Pongkemon01/weather-station/Inc/bsp_driver_sd.h

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
/* Define to prevent recursive inclusion -------------------------------------*/
#ifndef __STM32L4_SD_H
#define __STM32L4_SD_H

#ifdef __cplusplus
extern "C"
{
#endif

/* Includes ------------------------------------------------------------------*/
#include "stm32l4xx_hal.h"
#include "fatfs_platform.h"

/* Exported types ------------------------------------------------------------*/

/**
 * @brief SD Card information structure
 */
#define BSP_SD_CardInfo HAL_SD_CardInfoTypeDef

/* Exported constants --------------------------------------------------------*/
/**
 * @brief  SD status structure definition
 */
#define MSD_OK ((uint8_t)0x00)
#define MSD_ERROR ((uint8_t)0x01)
#define MSD_ERROR_SD_NOT_PRESENT ((uint8_t)0x02)

/**
 * @brief  SD transfer state definition
 */
#define SD_TRANSFER_OK ((uint8_t)0x00)
#define SD_TRANSFER_BUSY ((uint8_t)0x01)
#define SD_TRANSFER_ERROR ((uint8_t)0x02)

#define SD_DATATIMEOUT ((uint32_t)100000000)

#define SD_PRESENT ((uint8_t)0x01)
#define SD_NOT_PRESENT ((uint8_t)0x00)

#ifdef OLD_API
/* kept to avoid issue when migrating old projects. */
#else
/* USER CODE BEGIN BSP_H_CODE */
/* Exported functions --------------------------------------------------------*/
uint8_t BSP_SD_Init(void);
uint8_t BSP_SD_ITConfig(void);
void BSP_SD_DetectIT(void);
void BSP_SD_DetectCallback(void);
uint8_t BSP_SD_ReadBlocks(uint32_t *pData, uint32_t ReadAddr, uint32_t NumOfBlocks, uint32_t Timeout);
uint8_t BSP_SD_WriteBlocks(uint32_t *pData, uint32_t WriteAddr, uint32_t NumOfBlocks, uint32_t Timeout);
uint8_t BSP_SD_ReadBlocks_DMA(uint32_t *pData, uint32_t ReadAddr, uint32_t NumOfBlocks);
uint8_t BSP_SD_WriteBlocks_DMA(uint32_t *pData, uint32_t WriteAddr, uint32_t NumOfBlocks);
uint8_t BSP_SD_Erase(uint32_t StartAddr, uint32_t EndAddr);
uint8_t BSP_SD_GetCardState(void);
void BSP_SD_GetCardInfo(BSP_SD_CardInfo *CardInfo);
uint8_t BSP_SD_IsDetected(void);
/* USER CODE END BSP_H_CODE */
#endif
  /* USER CODE BEGIN CallBacksSection_H */
  /* These __weak functions can be surcharged by application code in case the current settings
     (eg. interrupt priority, callbacks implementation) need to be changed for specific application needs */
  void BSP_SD_AbortCallback(void);
  void BSP_SD_WriteCpltCallback(void);
  void BSP_SD_ReadCpltCallback(void);

  void BSP_SD_DMA_Tx_IRQHandler(void);
  void BSP_SD_DMA_Rx_IRQHandler(void);
/* USER CODE END CallBacksSection_H */
#ifdef __cplusplus
}
#endif

#endif /* __STM32L4_SD_H */
