Pongkemon01/weather-station/Src/sdmmc.c

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
/* Includes ------------------------------------------------------------------*/
#include "sdmmc.h"

/* USER CODE BEGIN 0 */
DMA_HandleTypeDef hdma_sdmmc1;
/* USER CODE END 0 */

SD_HandleTypeDef hsd1;
DMA_HandleTypeDef hdma_sdmmc1_rx;
DMA_HandleTypeDef hdma_sdmmc1_tx;

/* SDMMC1 init function */

void MX_SDMMC1_SD_Init(void)
{

  hsd1.Instance = SDMMC1;
  hsd1.Init.ClockEdge = SDMMC_CLOCK_EDGE_RISING;
  hsd1.Init.ClockBypass = SDMMC_CLOCK_BYPASS_DISABLE;
  hsd1.Init.ClockPowerSave = SDMMC_CLOCK_POWER_SAVE_DISABLE;
  hsd1.Init.BusWide = SDMMC_BUS_WIDE_4B;
  hsd1.Init.HardwareFlowControl = SDMMC_HARDWARE_FLOW_CONTROL_DISABLE;
  hsd1.Init.ClockDiv = 16;
}

void HAL_SD_MspInit(SD_HandleTypeDef *sdHandle)
{

  GPIO_InitTypeDef GPIO_InitStruct = {0};
  if (sdHandle->Instance == SDMMC1)
  {
    /* USER CODE BEGIN SDMMC1_MspInit 0 */

    /* SDMMC1 clock enable */
    __HAL_RCC_SDMMC1_CLK_ENABLE();

    __HAL_RCC_GPIOC_CLK_ENABLE();
    __HAL_RCC_GPIOD_CLK_ENABLE();
    /**SDMMC1 GPIO Configuration
    PC8     ------> SDMMC1_D0
    PC9     ------> SDMMC1_D1
    PC10     ------> SDMMC1_D2
    PC11     ------> SDMMC1_D3
    PC12     ------> SDMMC1_CK
    PD2     ------> SDMMC1_CMD
    */
    GPIO_InitStruct.Pin = GPIO_PIN_8 | GPIO_PIN_9 | GPIO_PIN_10 | GPIO_PIN_11 | GPIO_PIN_12;
    GPIO_InitStruct.Mode = GPIO_MODE_AF_PP;
    GPIO_InitStruct.Pull = GPIO_NOPULL;
    GPIO_InitStruct.Speed = GPIO_SPEED_FREQ_VERY_HIGH;
    GPIO_InitStruct.Alternate = GPIO_AF12_SDMMC1;
    HAL_GPIO_Init(GPIOC, &GPIO_InitStruct);

    GPIO_InitStruct.Pin = GPIO_PIN_2;
    GPIO_InitStruct.Mode = GPIO_MODE_AF_PP;
    GPIO_InitStruct.Pull = GPIO_NOPULL;
    GPIO_InitStruct.Speed = GPIO_SPEED_FREQ_VERY_HIGH;
    GPIO_InitStruct.Alternate = GPIO_AF12_SDMMC1;
    HAL_GPIO_Init(GPIOD, &GPIO_InitStruct);

    //  Replace both hdma_sdmmc1_rx and hdma_sdmmc1_tx with a single handle

    // In HAL_SD_MspInit():
    hdma_sdmmc1.Instance = DMA2_Channel4;
    hdma_sdmmc1.Init.Request = DMA_REQUEST_7;
    hdma_sdmmc1.Init.Direction = DMA_MEMORY_TO_PERIPH;
    hdma_sdmmc1.Init.PeriphInc = DMA_PINC_DISABLE;
    hdma_sdmmc1.Init.MemInc = DMA_MINC_ENABLE;
    hdma_sdmmc1.Init.PeriphDataAlignment = DMA_PDATAALIGN_WORD;
    hdma_sdmmc1.Init.MemDataAlignment = DMA_MDATAALIGN_WORD;
    hdma_sdmmc1.Init.Mode = DMA_NORMAL;
    hdma_sdmmc1.Init.Priority = DMA_PRIORITY_HIGH;
    // Note: Direction gets set internally by HAL_SD before each transfer,
    // so a single static Direction field here isn't used the same way —
    // HAL_SD_Read/WriteBlocks_DMA reconfigure direction via SDMMC_DMA APIs.
    if (HAL_DMA_Init(&hdma_sdmmc1) != HAL_OK)
    {
      Error_Handler();
    }

    /* Several peripheral DMA handle pointers point to the same DMA handle.
     Be aware that there is only one channel to perform all the requested DMAs. */
    __HAL_LINKDMA(sdHandle, hdmarx, hdma_sdmmc1);
    __HAL_LINKDMA(sdHandle, hdmatx, hdma_sdmmc1);

    HAL_NVIC_SetPriority(SDMMC1_IRQn, 5, 0);
    HAL_NVIC_EnableIRQ(SDMMC1_IRQn);

#if 0

  /* USER CODE END SDMMC1_MspInit 0 */
    /* SDMMC1 clock enable */
    __HAL_RCC_SDMMC1_CLK_ENABLE();

    __HAL_RCC_GPIOC_CLK_ENABLE();
    __HAL_RCC_GPIOD_CLK_ENABLE();
    /**SDMMC1 GPIO Configuration
    PC8     ------> SDMMC1_D0
    PC9     ------> SDMMC1_D1
    PC10     ------> SDMMC1_D2
    PC11     ------> SDMMC1_D3
    PC12     ------> SDMMC1_CK
    PD2     ------> SDMMC1_CMD
    */
    GPIO_InitStruct.Pin = GPIO_PIN_8|GPIO_PIN_9|GPIO_PIN_10|GPIO_PIN_11
                          |GPIO_PIN_12;
    GPIO_InitStruct.Mode = GPIO_MODE_AF_PP;
    GPIO_InitStruct.Pull = GPIO_NOPULL;
    GPIO_InitStruct.Speed = GPIO_SPEED_FREQ_VERY_HIGH;
    GPIO_InitStruct.Alternate = GPIO_AF12_SDMMC1;
    HAL_GPIO_Init(GPIOC, &GPIO_InitStruct);

    GPIO_InitStruct.Pin = GPIO_PIN_2;
    GPIO_InitStruct.Mode = GPIO_MODE_AF_PP;
    GPIO_InitStruct.Pull = GPIO_NOPULL;
    GPIO_InitStruct.Speed = GPIO_SPEED_FREQ_VERY_HIGH;
    GPIO_InitStruct.Alternate = GPIO_AF12_SDMMC1;
    HAL_GPIO_Init(GPIOD, &GPIO_InitStruct);

    /* SDMMC1 DMA Init */
    /* SDMMC1_RX Init */
    hdma_sdmmc1_rx.Instance = DMA2_Channel4;
    hdma_sdmmc1_rx.Init.Request = DMA_REQUEST_7;
    hdma_sdmmc1_rx.Init.Direction = DMA_PERIPH_TO_MEMORY;
    hdma_sdmmc1_rx.Init.PeriphInc = DMA_PINC_DISABLE;
    hdma_sdmmc1_rx.Init.MemInc = DMA_MINC_ENABLE;
    hdma_sdmmc1_rx.Init.PeriphDataAlignment = DMA_PDATAALIGN_WORD;
    hdma_sdmmc1_rx.Init.MemDataAlignment = DMA_MDATAALIGN_WORD;
    hdma_sdmmc1_rx.Init.Mode = DMA_NORMAL;
    hdma_sdmmc1_rx.Init.Priority = DMA_PRIORITY_HIGH;
    if (HAL_DMA_Init(&hdma_sdmmc1_rx) != HAL_OK)
    {
      Error_Handler();
    }

    __HAL_LINKDMA(sdHandle,hdmarx,hdma_sdmmc1_rx);

    /* SDMMC1_TX Init */
    hdma_sdmmc1_tx.Instance = DMA2_Channel5;
    hdma_sdmmc1_tx.Init.Request = DMA_REQUEST_7;
    hdma_sdmmc1_tx.Init.Direction = DMA_MEMORY_TO_PERIPH;
    hdma_sdmmc1_tx.Init.PeriphInc = DMA_PINC_DISABLE;
    hdma_sdmmc1_tx.Init.MemInc = DMA_MINC_ENABLE;
    hdma_sdmmc1_tx.Init.PeriphDataAlignment = DMA_PDATAALIGN_WORD;
    hdma_sdmmc1_tx.Init.MemDataAlignment = DMA_MDATAALIGN_WORD;
    hdma_sdmmc1_tx.Init.Mode = DMA_NORMAL;
    hdma_sdmmc1_tx.Init.Priority = DMA_PRIORITY_HIGH;
    if (HAL_DMA_Init(&hdma_sdmmc1_tx) != HAL_OK)
    {
      Error_Handler();
    }

    __HAL_LINKDMA(sdHandle,hdmatx,hdma_sdmmc1_tx);

    /* SDMMC1 interrupt Init */
    HAL_NVIC_SetPriority(SDMMC1_IRQn, 5, 0);
    HAL_NVIC_EnableIRQ(SDMMC1_IRQn);
  /* USER CODE BEGIN SDMMC1_MspInit 1 */
#endif
    /* USER CODE END SDMMC1_MspInit 1 */
  }
}

void HAL_SD_MspDeInit(SD_HandleTypeDef *sdHandle)
{

  if (sdHandle->Instance == SDMMC1)
  {
    /* USER CODE BEGIN SDMMC1_MspDeInit 0 */
    /* Peripheral clock disable */
    __HAL_RCC_SDMMC1_CLK_DISABLE();

    /**SDMMC1 GPIO Configuration
    PC8     ------> SDMMC1_D0
    PC9     ------> SDMMC1_D1
    PC10     ------> SDMMC1_D2
    PC11     ------> SDMMC1_D3
    PC12     ------> SDMMC1_CK
    PD2     ------> SDMMC1_CMD
    */
    HAL_GPIO_DeInit(GPIOC, GPIO_PIN_8 | GPIO_PIN_9 | GPIO_PIN_10 | GPIO_PIN_11 | GPIO_PIN_12);

    HAL_GPIO_DeInit(GPIOD, GPIO_PIN_2);

    /* SDMMC1 DMA DeInit */
    HAL_DMA_DeInit(sdHandle->hdmarx);
    HAL_DMA_DeInit(sdHandle->hdmatx);

    /* SDMMC1 interrupt Deinit */
    HAL_NVIC_DisableIRQ(SDMMC1_IRQn);
#if 0
  /* USER CODE END SDMMC1_MspDeInit 0 */
    /* Peripheral clock disable */
    __HAL_RCC_SDMMC1_CLK_DISABLE();

    /**SDMMC1 GPIO Configuration
    PC8     ------> SDMMC1_D0
    PC9     ------> SDMMC1_D1
    PC10     ------> SDMMC1_D2
    PC11     ------> SDMMC1_D3
    PC12     ------> SDMMC1_CK
    PD2     ------> SDMMC1_CMD
    */
    HAL_GPIO_DeInit(GPIOC, GPIO_PIN_8|GPIO_PIN_9|GPIO_PIN_10|GPIO_PIN_11
                          |GPIO_PIN_12);

    HAL_GPIO_DeInit(GPIOD, GPIO_PIN_2);

    /* SDMMC1 DMA DeInit */
    HAL_DMA_DeInit(sdHandle->hdmarx);
    HAL_DMA_DeInit(sdHandle->hdmatx);

    /* SDMMC1 interrupt Deinit */
    HAL_NVIC_DisableIRQ(SDMMC1_IRQn);
  /* USER CODE BEGIN SDMMC1_MspDeInit 1 */
#endif
    /* USER CODE END SDMMC1_MspDeInit 1 */
  }
}
