Pongkemon01/weather-station/Src/rtc.c

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
/* Includes ------------------------------------------------------------------*/
#include "rtc.h"

RTC_HandleTypeDef hrtc;

/* RTC init function */
void MX_RTC_Init(void)
{

    RTC_TimeTypeDef sTime = {0};
    RTC_DateTypeDef sDate = {0};

    /** Initialize RTC Only
     */
    hrtc.Instance = RTC;
    hrtc.Init.HourFormat = RTC_HOURFORMAT_24;
    hrtc.Init.AsynchPrediv = 127;
    hrtc.Init.SynchPrediv = 255;
    hrtc.Init.OutPut = RTC_OUTPUT_DISABLE;
    hrtc.Init.OutPutRemap = RTC_OUTPUT_REMAP_NONE;
    hrtc.Init.OutPutPolarity = RTC_OUTPUT_POLARITY_HIGH;
    hrtc.Init.OutPutType = RTC_OUTPUT_TYPE_OPENDRAIN;
    if (HAL_RTC_Init(&hrtc) != HAL_OK)
    {
        Error_Handler();
    }

    /** Initialize RTC and set the Time and Date
     */
    // sTime.Hours = 0;
    // sTime.Minutes = 0;
    // sTime.Seconds = 0;
    // sTime.DayLightSaving = RTC_DAYLIGHTSAVING_NONE;
    // sTime.StoreOperation = RTC_STOREOPERATION_RESET;
    // if (HAL_RTC_SetTime(&hrtc, &sTime, RTC_FORMAT_BIN) != HAL_OK)
    // {
    //     Error_Handler();
    // }
    // sDate.WeekDay = RTC_WEEKDAY_THURSDAY;
    // sDate.Month = RTC_MONTH_JANUARY;
    // sDate.Date = 1;
    // sDate.Year = 26;

    // if (HAL_RTC_SetDate(&hrtc, &sDate, RTC_FORMAT_BIN) != HAL_OK)
    // {
    //     Error_Handler();
    // }
    /* USER CODE BEGIN RTC_Init 2 */

    // Configure wakeup timer: 1 Hz clock source, counter = 2047 → period = 1 second
    // DO NOT enable NVIC here — maintask() will call HAL_NVIC_EnableIRQ()
    // Reference: RM0351 §38.5.6, stm32l4xx_hal_rtc_ex.c
    if (HAL_RTCEx_SetWakeUpTimer_IT(&hrtc, 2047,
                                    RTC_WAKEUPCLOCK_RTCCLK_DIV16) != HAL_OK)
    {
        Error_Handler();
    }

    /* USER CODE END RTC_Init 2 */
}

void HAL_RTC_MspInit(RTC_HandleTypeDef *rtcHandle)
{

    RCC_PeriphCLKInitTypeDef PeriphClkInit = {0};
    if (rtcHandle->Instance == RTC)
    {
        /** Initializes the peripherals clock
         */
        PeriphClkInit.PeriphClockSelection = RCC_PERIPHCLK_RTC;
        PeriphClkInit.RTCClockSelection = RCC_RTCCLKSOURCE_LSE;
        if (HAL_RCCEx_PeriphCLKConfig(&PeriphClkInit) != HAL_OK)
        {
            Error_Handler();
        }

        /* RTC clock enable */
        __HAL_RCC_RTC_ENABLE();

        /* RTC interrupt Init */
        HAL_NVIC_SetPriority(RTC_WKUP_IRQn, 5, 0);
        // HAL_NVIC_EnableIRQ(RTC_WKUP_IRQn); /* Will be enabled by user later */
    }
}

void HAL_RTC_MspDeInit(RTC_HandleTypeDef *rtcHandle)
{

    if (rtcHandle->Instance == RTC)
    {
        /* Peripheral clock disable */
        __HAL_RCC_RTC_DISABLE();

        /* RTC interrupt Deinit */
        HAL_NVIC_DisableIRQ(RTC_WKUP_IRQn);
    }
}
